levon-m/microloop/hardware/schematics/microloop.kicad_sch

## KiCad design hardware/schematics/microloop.kicad_sch (2025-12-10)

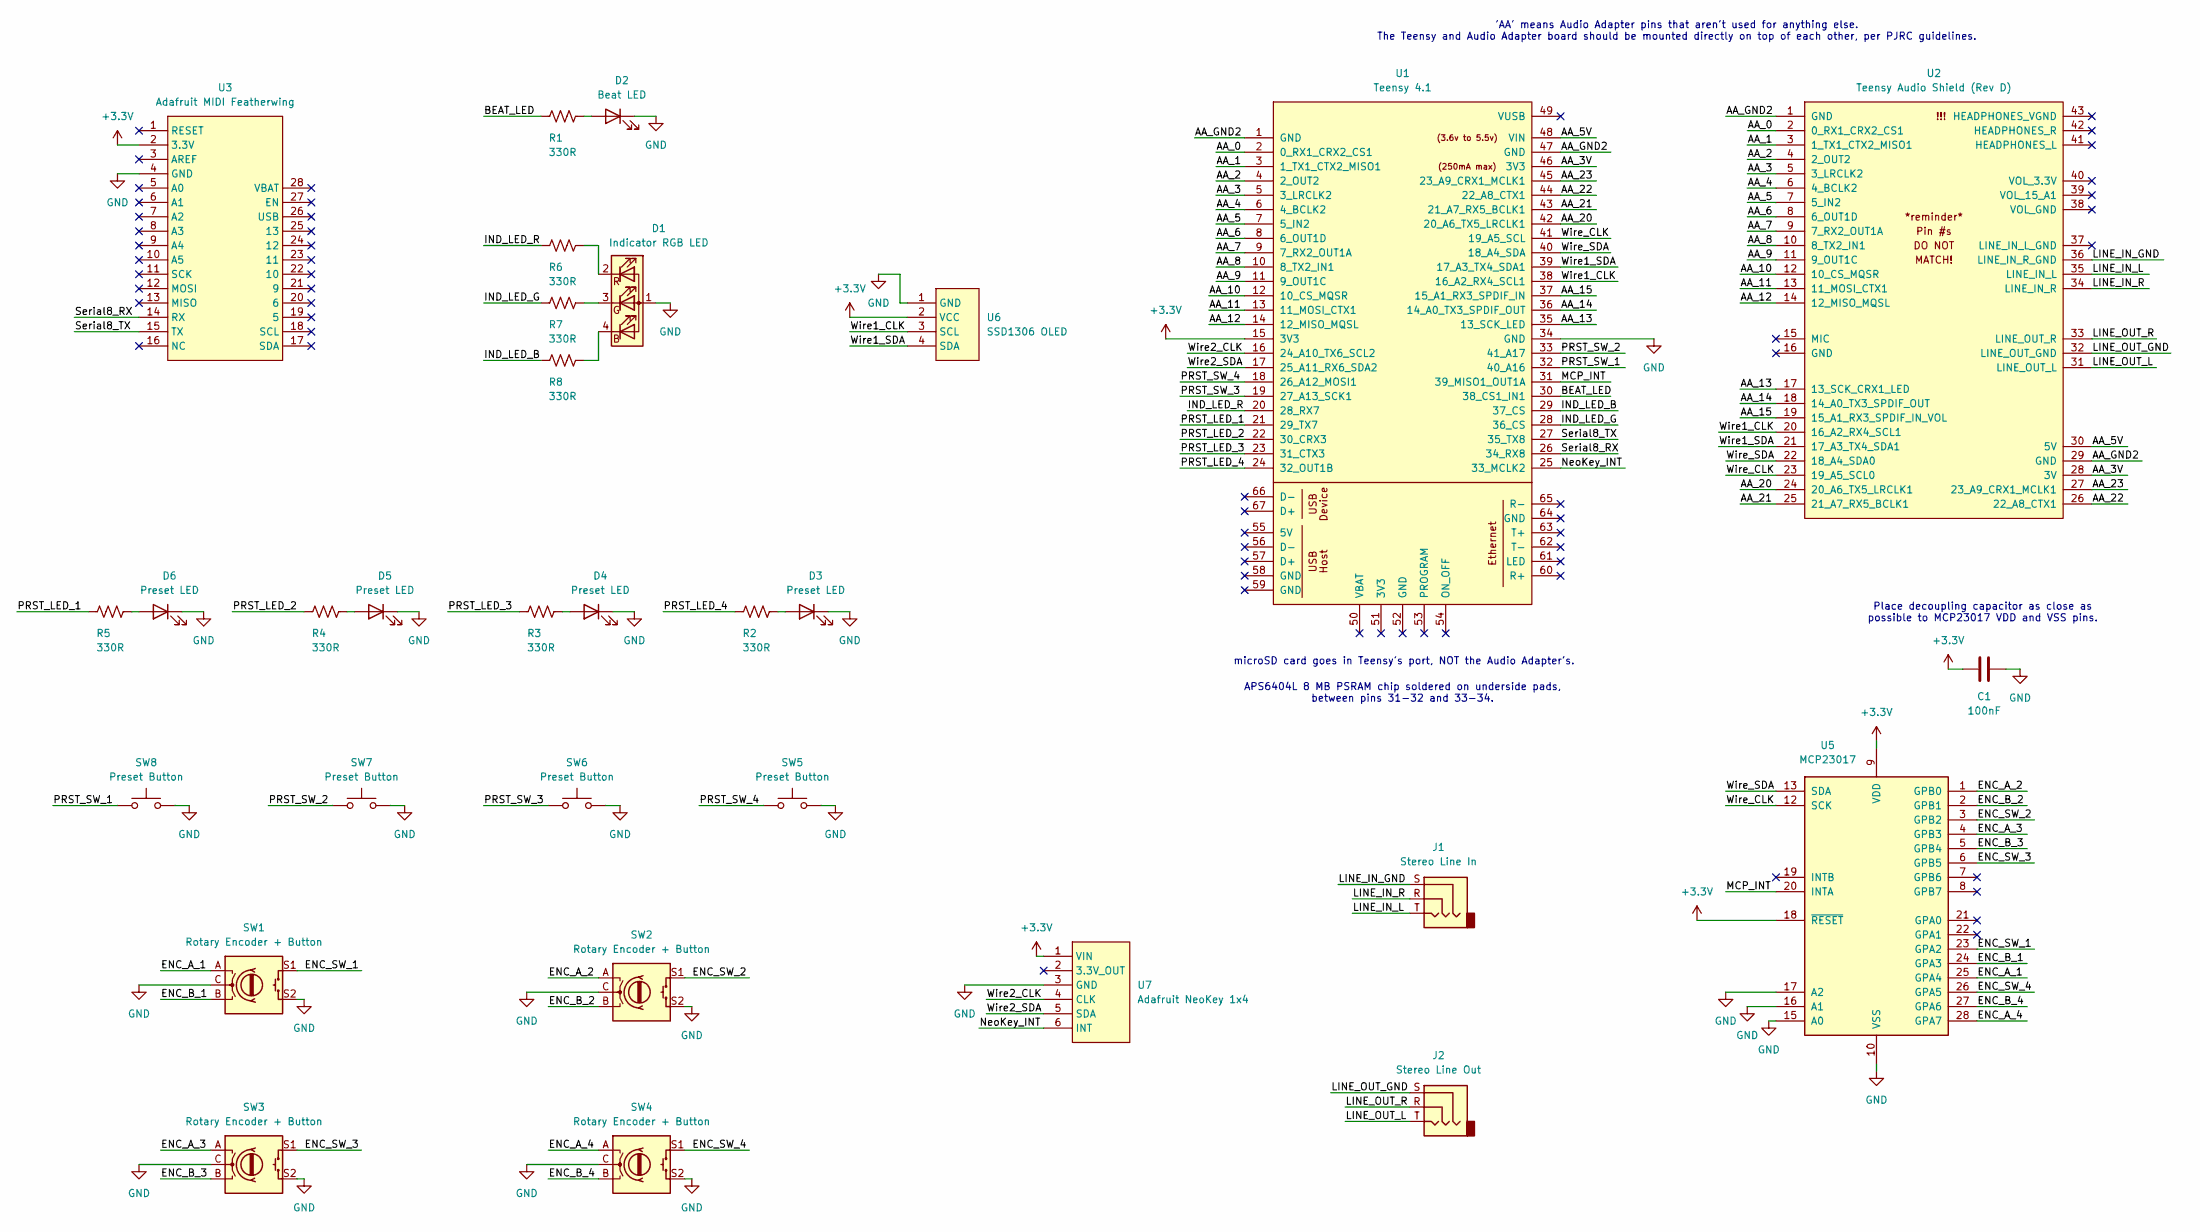
[picture p3: schematic microloop.kicad_sch]

Parts:
C1: 100nF
D1: Indicator RGB LED
D2: Beat LED
D3, D4, D5, D6: Preset LED
J1: Stereo Line In
J2: Stereo Line Out
R1, R2, R3, R4, R5, R6, R7, R8: 330R
SW1, SW2, SW3, SW4: Rotary Encoder + Button
SW5, SW6, SW7, SW8: Preset Button
U1: Teensy 4.1
U2: Teensy Audio Shield (Rev D)
U3: Adafruit MIDI Featherwing
U5: MCP23017; SOIC-28W_7.5x17.9mm_P1.27mm
U6: SSD1306 OLED
U7: Adafruit NeoKey 1x4

Connections:
+3.3V: C1.1, U1.15 (3V3), U3.2 (3.3V), U5.9 (VDD), U5.18 (~RESET), U6.2 (VCC), U7.1 (VIN)
AA_0: U1.2 (0_RX1_CRX2_CS1), U2.2 (0_RX1_CRX2_CS1)
AA_1: U1.3 (1_TX1_CTX2_MISO1), U2.3 (1_TX1_CTX2_MISO1)
AA_2: U1.4 (2_OUT2), U2.4 (2_OUT2)
AA_3: U1.5 (3_LRCLK2), U2.5 (3_LRCLK2)
AA_3V: U1.46 (3V3), U2.28 (3V)
AA_4: U1.6 (4_BCLK2), U2.6 (4_BCLK2)
AA_5: U1.7 (5_IN2), U2.7 (5_IN2)
AA_5V: U1.48 (VIN), U2.30 (5V)
AA_6: U1.8 (6_OUT1D), U2.8 (6_OUT1D)
AA_7: U1.9 (7_RX2_OUT1A), U2.9 (7_RX2_OUT1A)
AA_8: U1.10 (8_TX2_IN1), U2.10 (8_TX2_IN1)
AA_9: U1.11 (9_OUT1C), U2.11 (9_OUT1C)
AA_10: U1.12 (10_CS_MQSR), U2.12 (10_CS_MQSR)
AA_11: U1.13 (11_MOSI_CTX1), U2.13 (11_MOSI_CTX1)
AA_12: U1.14 (12_MISO_MQSL), U2.14 (12_MISO_MQSL)
AA_13: U1.35 (13_SCK_LED), U2.17 (13_SCK_CRX1_LED)
AA_14: U1.36 (14_A0_TX3_SPDIF_OUT), U2.18 (14_A0_TX3_SPDIF_OUT)
AA_15: U1.37 (15_A1_RX3_SPDIF_IN), U2.19 (15_A1_RX3_SPDIF_IN_VOL)
AA_20: U1.42 (20_A6_TX5_LRCLK1), U2.24 (20_A6_TX5_LRCLK1)
AA_21: U1.43 (21_A7_RX5_BCLK1), U2.25 (21_A7_RX5_BCLK1)
AA_22: U1.44 (22_A8_CTX1), U2.26 (22_A8_CTX1)
AA_23: U1.45 (23_A9_CRX1_MCLK1), U2.27 (23_A9_CRX1_MCLK1)
AA_GND2: U1.1 (GND), U1.47 (GND), U2.1 (GND), U2.29 (GND)
BEAT_LED: R1.2, U1.30 (38_CS1_IN1)
ENC_A_1: SW1.A, U5.25 (GPA4)
ENC_A_2: SW2.A, U5.1 (GPB0)
ENC_A_3: SW3.A, U5.4 (GPB3)
ENC_A_4: SW4.A, U5.28 (GPA7)
ENC_B_1: SW1.B, U5.24 (GPA3)
ENC_B_2: SW2.B, U5.2 (GPB1)
ENC_B_3: SW3.B, U5.5 (GPB4)
ENC_B_4: SW4.B, U5.27 (GPA6)
ENC_SW_1: SW1.S1, U5.23 (GPA2)
ENC_SW_2: SW2.S1, U5.3 (GPB2)
ENC_SW_3: SW3.S1, U5.6 (GPB5)
ENC_SW_4: SW4.S1, U5.26 (GPA5)
GND: C1.2, D1.1 (A), D2.1 (K), D3.1 (K), D4.1 (K), D5.1 (K), D6.1 (K), SW1.C, SW1.S2, SW2.C, SW2.S2, SW3.C, SW3.S2, SW4.C, SW4.S2, SW5.1, SW6.1, SW7.1, SW8.1, U1.34 (GND), U3.4 (GND), U5.10 (VSS), U5.15 (A0), U5.16 (A1), U5.17 (A2), U6.1 (GND), U7.3 (GND)
IND_LED_B: R8.2, U1.29 (37_CS)
IND_LED_G: R7.2, U1.28 (36_CS)
IND_LED_R: R6.2, U1.20 (28_RX7)
LINE_IN_GND: J1.S, U2.36 (LINE_IN_R_GND)
LINE_IN_L: J1.T, U2.35 (LINE_IN_L)
LINE_IN_R: J1.R, U2.34 (LINE_IN_R)
LINE_OUT_GND: J2.S, U2.32 (LINE_OUT_GND)
LINE_OUT_L: J2.T, U2.31 (LINE_OUT_L)
LINE_OUT_R: J2.R, U2.33 (LINE_OUT_R)
MCP_INT: U1.31 (39_MISO1_OUT1A), U5.20 (INTA)
NeoKey_INT: U1.25 (33_MCLK2), U7.6 (INT)
unnamed: D1.2 (RK), R6.1
unnamed: D1.3 (GK), R7.1
unnamed: D1.4 (BK), R8.1
unnamed: D2.2 (A), R1.1
unnamed: D3.2 (A), R2.1
unnamed: D4.2 (A), R3.1
unnamed: D5.2 (A), R4.1
unnamed: D6.2 (A), R5.1
PRST_LED_1: R5.2, U1.21 (29_TX7)
PRST_LED_2: R4.2, U1.22 (30_CRX3)
PRST_LED_3: R3.2, U1.23 (31_CTX3)
PRST_LED_4: R2.2, U1.24 (32_OUT1B)
PRST_SW_1: SW8.2, U1.32 (40_A16)
PRST_SW_2: SW7.2, U1.33 (41_A17)
PRST_SW_3: SW6.2, U1.19 (27_A13_SCK1)
PRST_SW_4: SW5.2, U1.18 (26_A12_MOSI1)
Serial8_RX: U1.26 (34_RX8), U3.14 (RX)
Serial8_TX: U1.27 (35_TX8), U3.15 (TX)
Wire1_CLK: U1.38 (16_A2_RX4_SCL1), U2.20 (16_A2_RX4_SCL1), U6.3 (SCL)
Wire1_SDA: U1.39 (17_A3_TX4_SDA1), U2.21 (17_A3_TX4_SDA1), U6.4 (SDA)
Wire2_CLK: U1.16 (24_A10_TX6_SCL2), U7.4 (CLK)
Wire2_SDA: U1.17 (25_A11_RX6_SDA2), U7.5 (SDA)
Wire_CLK: U1.41 (19_A5_SCL), U2.23 (19_A5_SCL0), U5.12 (SCK)
Wire_SDA: U1.40 (18_A4_SDA), U2.22 (18_A4_SDA0), U5.13 (SDA)

Notes on the sheet:
Place decoupling capacitor as close as possible to MCP23017 VDD and VSS pins.
'AA' means Audio Adapter pins that aren't used for anything else. The Teensy and Audio Adapter board should be mounted directly on top of each other, per PJRC guidelines.
microSD card goes in Teensy's port, NOT the Audio Adapter's.
APS6404L 8 MB PSRAM chip soldered on underside pads, between pins 31-32 and 33-34.
